MLKiiwy/autonomous-outside-weather-station/elements/rain_counter_module/src/2_2_i2c_on_arduino_read_attiny_value/2_2_i2c_on_arduino_read_attiny_value.ino

#include <Wire.h>

#define ATTINY_I2C_ADDRESS 0x04
#define DELAY_BETWEEN_REQUEST 2000

uint8_t valueReceived = 0;

void setup() {
  Wire.begin(); // join i2c
  Serial.begin(9600); // start serial for debug
  Serial.println("starting");
}

void loop() {
  Wire.requestFrom(ATTINY_I2C_ADDRESS, 1);

  while (Wire.available()) {
    valueReceived = Wire.read();
    Serial.println(valueReceived);
  }
  
  delay(DELAY_BETWEEN_REQUEST);
}
